AppleJuice546/DIY-F16-ICP-Panel/STEP FILES/IPC WX key.stp

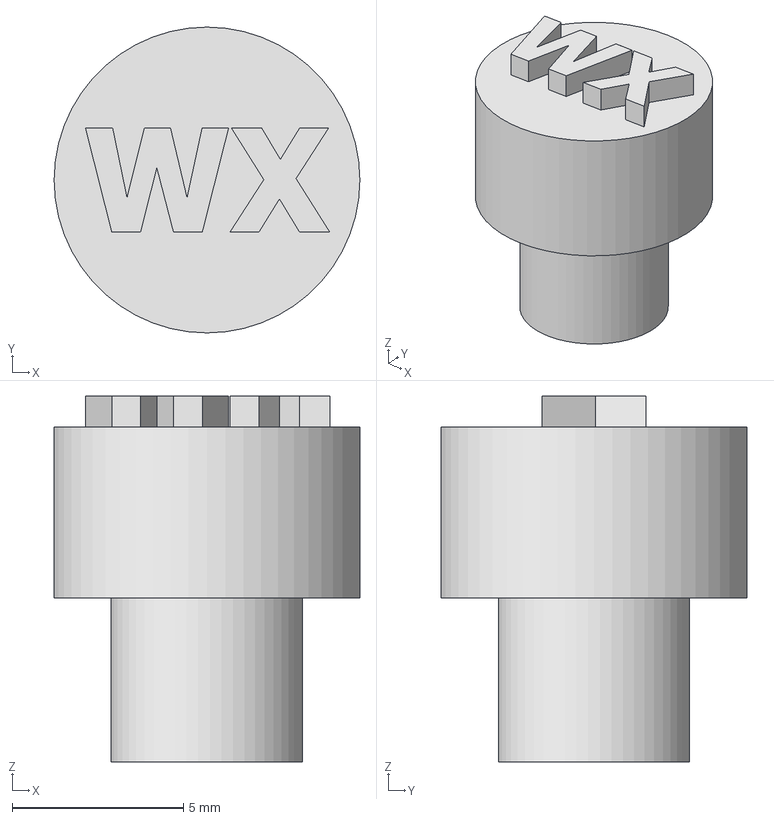
[picture p12: CAD file, 2022-01-09]
STEP FILES/IPC WX key.stp
8.94 x 8.94 x 10.7 mm
