AppleJuice546/DIY-F16-ICP-Panel/STEP FILES/IPC FIX 8.stp

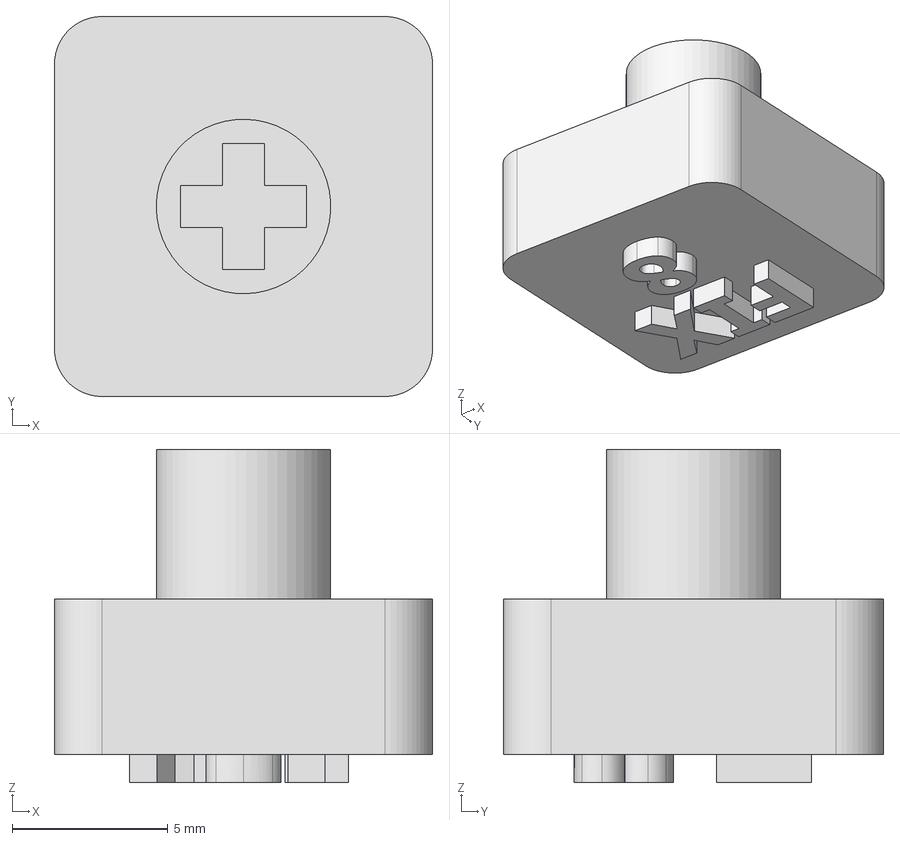
[picture p13: CAD file, 2022-01-09]
STEP FILES/IPC FIX 8.stp
12.1 x 12.2 x 10.7 mm
