AppleJuice546/DIY-F16-ICP-Panel/STEP FILES/IPC RCL key.stp

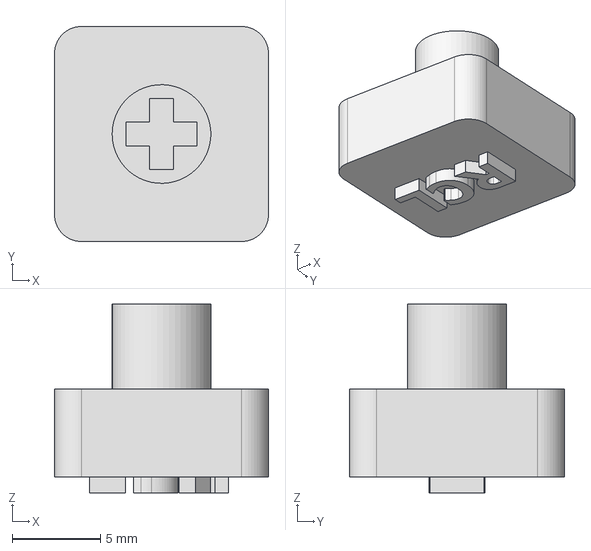
[picture p14: CAD file, 2022-01-09]
STEP FILES/IPC RCL key.stp
12.1 x 12.2 x 10.7 mm
