AppleJuice546/DIY-F16-ICP-Panel/STEP FILES/IPC Rear Panel v2.stp

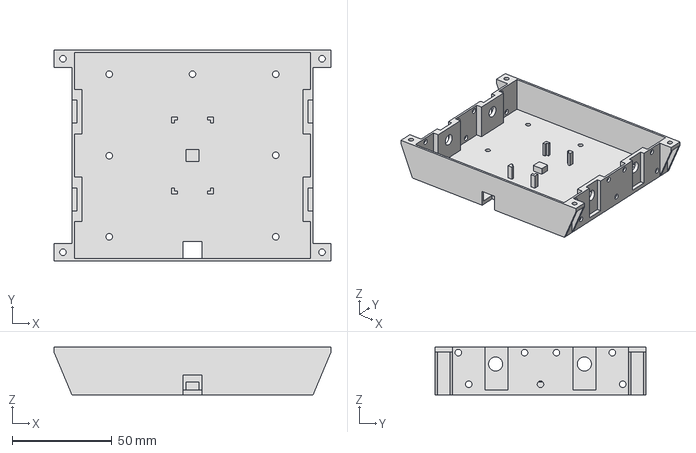
[picture p15: CAD file, 2022-01-09]
STEP FILES/IPC Rear Panel v2.stp
138.9 x 106.0 x 24.0 mm
